softegg/Vectorscope-Synth/Docs/vectorscope-synth-16x9-maybe-back.png

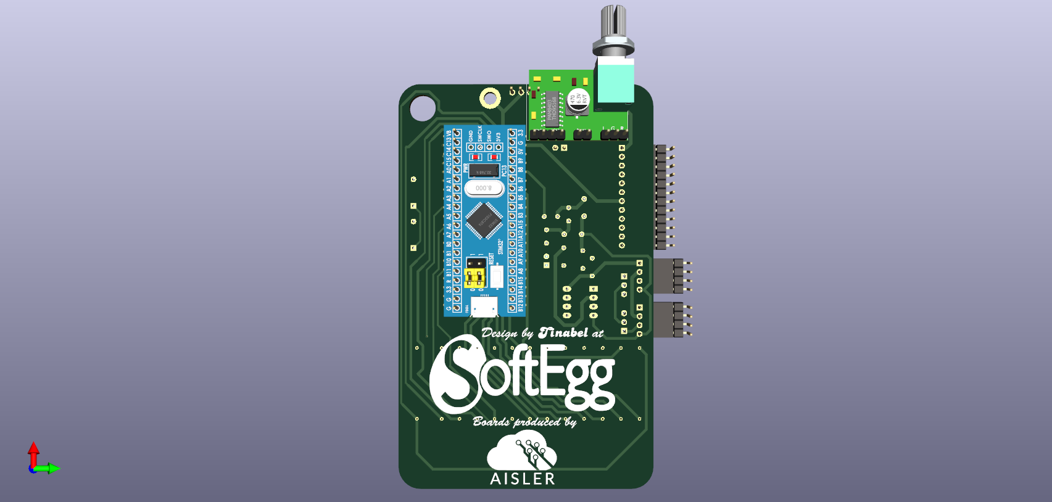
Docs/vectorscope-synth-16x9-maybe-back.png
