softegg/Vectorscope-Synth/Docs/vectorscope-synth-16x9-maybe.png

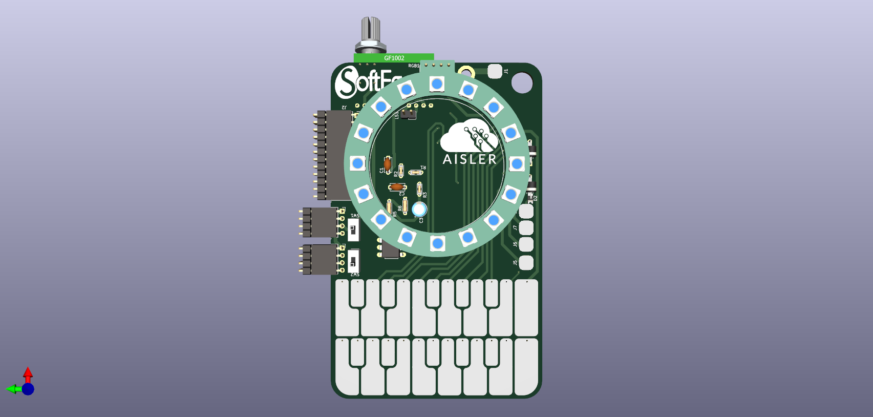
Docs/vectorscope-synth-16x9-maybe.png
